monotech/monotech_xt-cf-mini/Images/Front profile.png

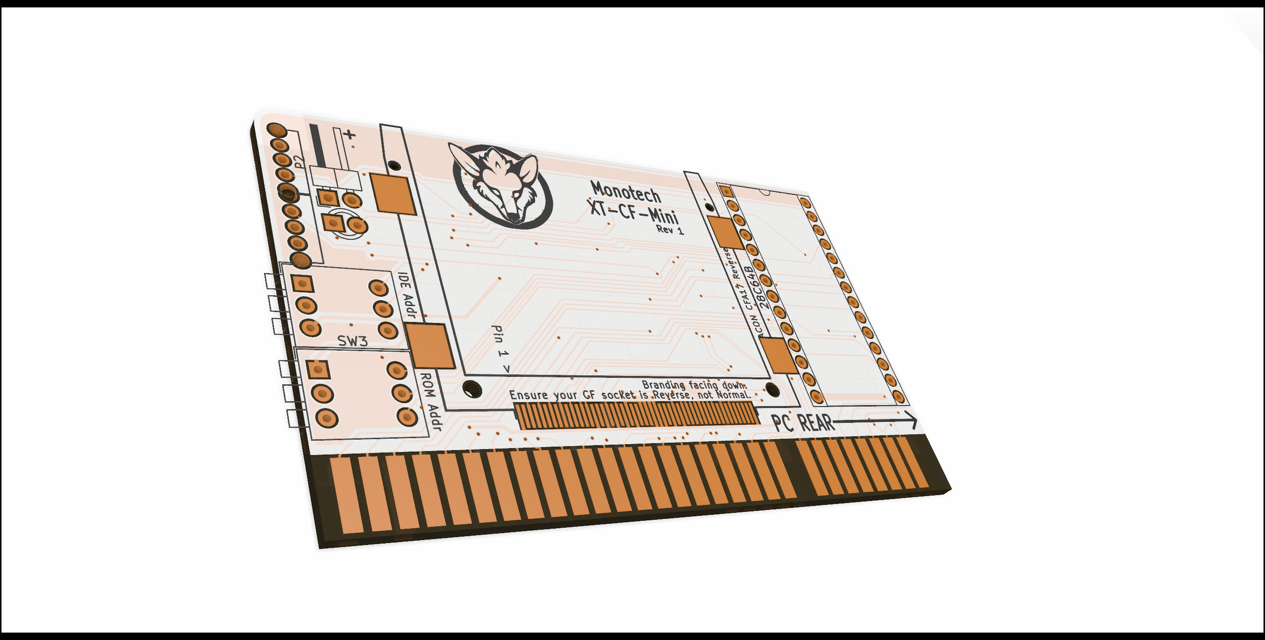
Images/Front profile.png
