monotech/monotech_xt-cf-mini/Photos/Back.jpg

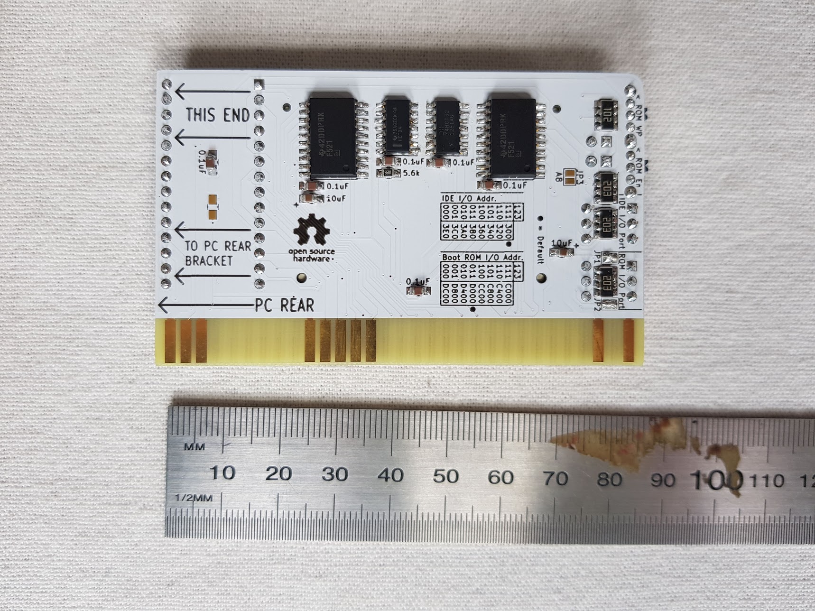
Photos/Back.jpg
