monotech/monotech_xt-cf-mini/Photos/Front.jpg

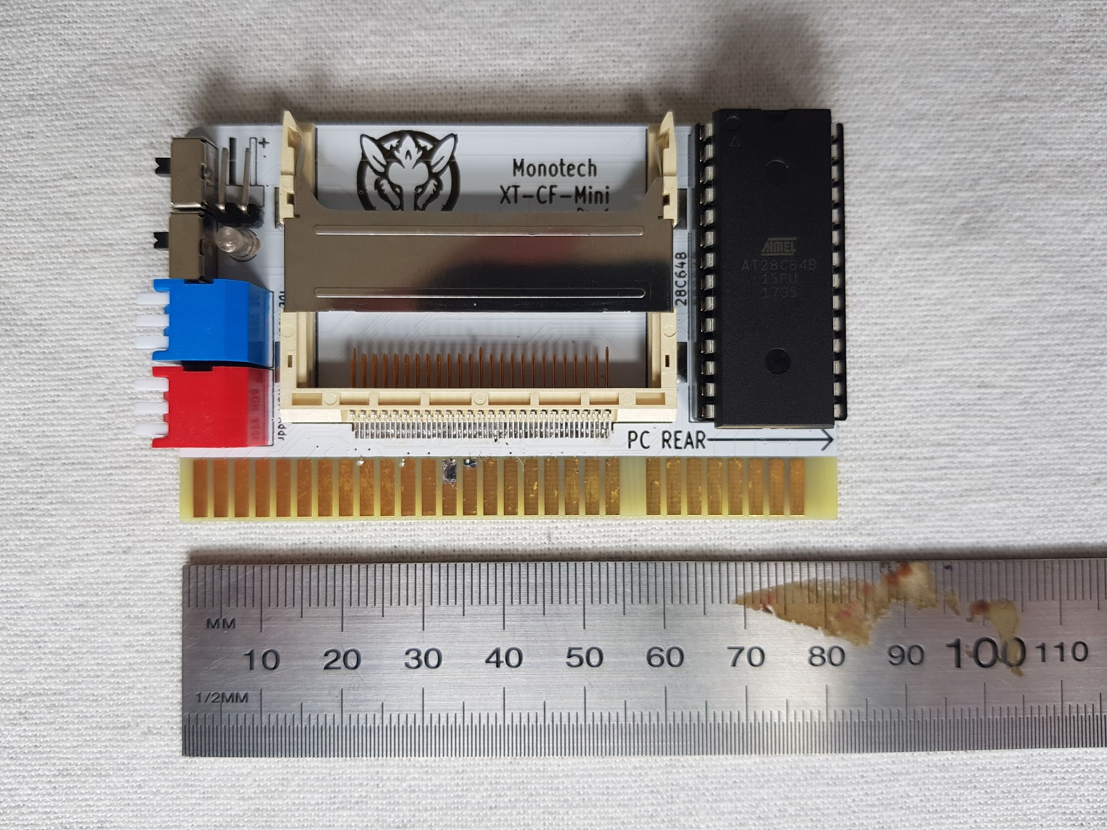
Photos/Front.jpg
