monotech/monotech_xt-cf-mini/Photos/In hand.jpg

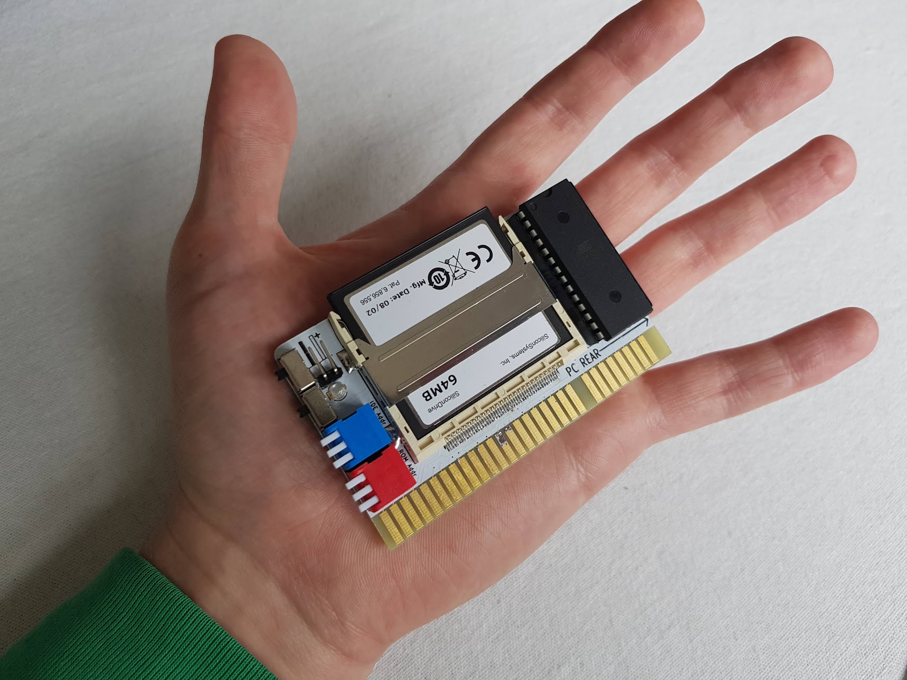
Photos/In hand.jpg
