monotech/monotech_xt-cf-mini/Photos/In motherboard - profile.jpg

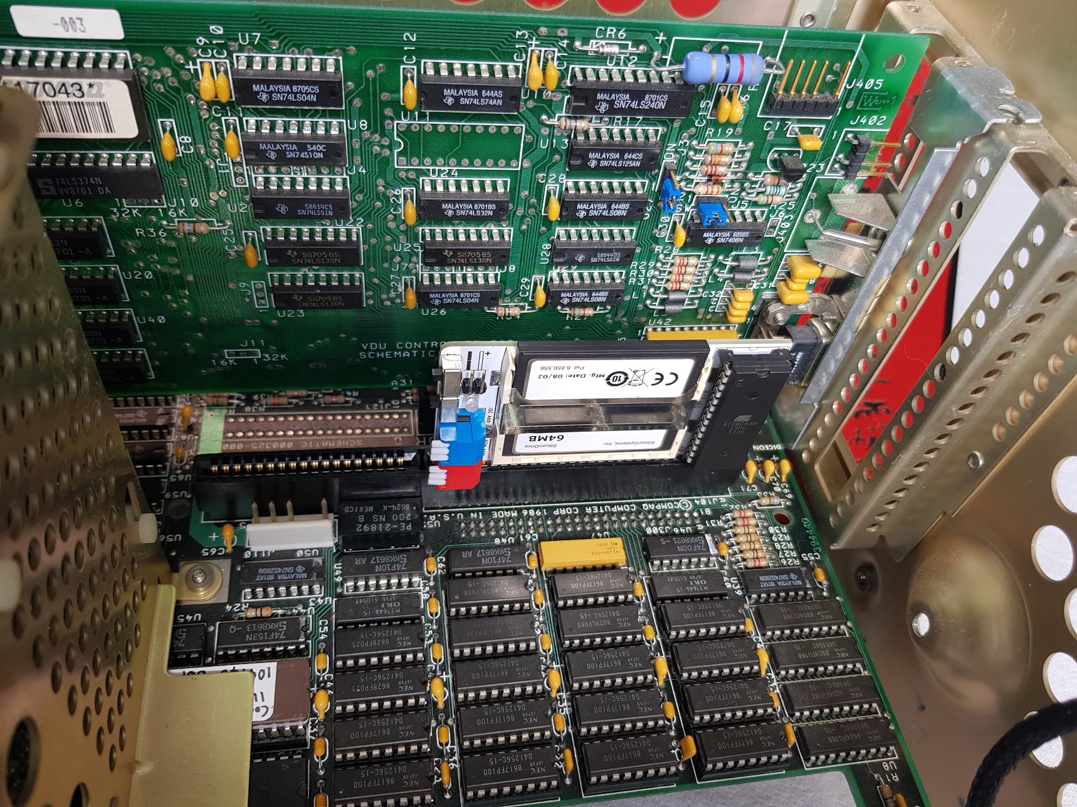
Photos/In motherboard - profile.jpg
