monotech/monotech_xt-cf-mini/Photos/In motherboard - side.jpg

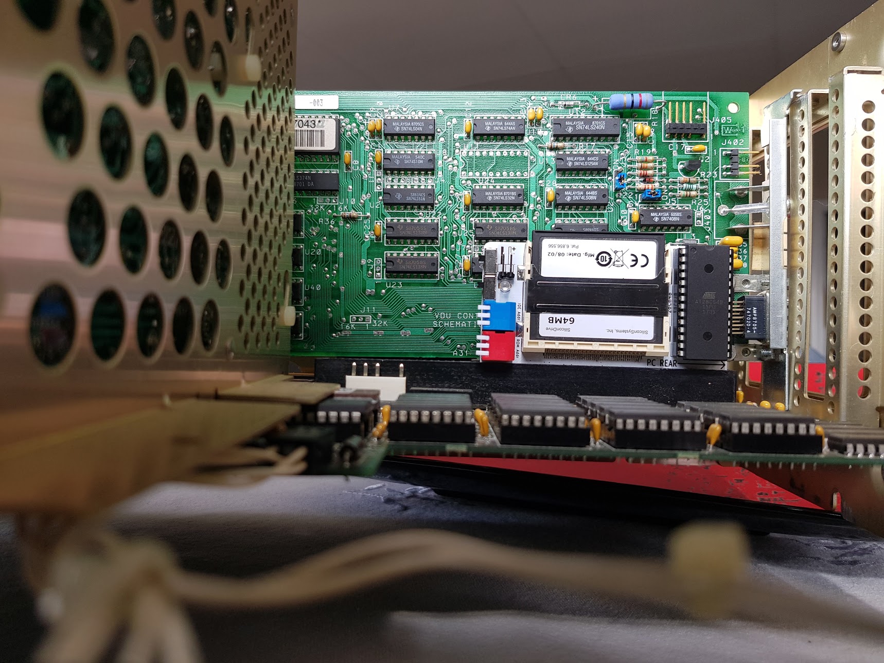
Photos/In motherboard - side.jpg
