monotech/monotech_xt-cf-mini/Images/Front with some parts models.png

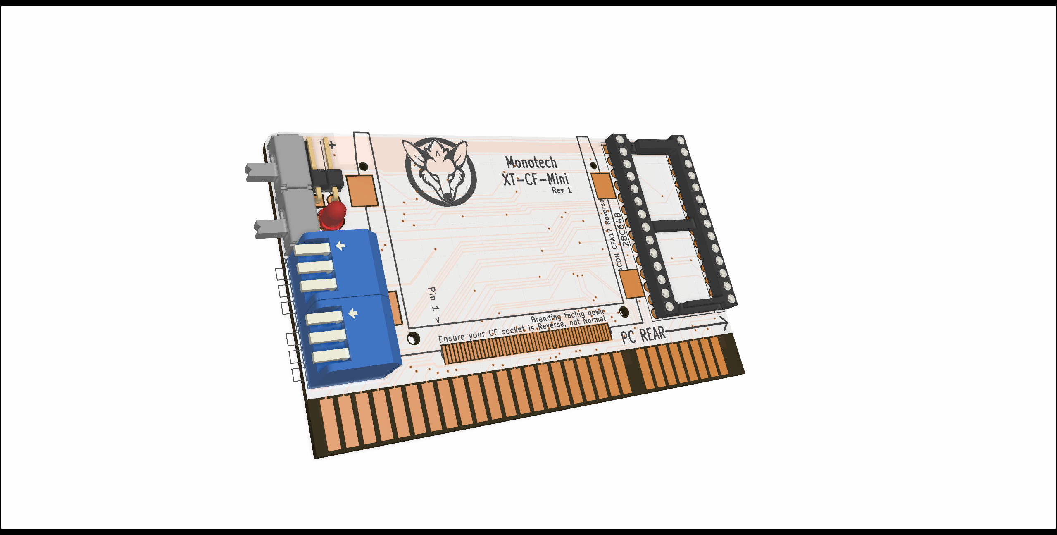
Images/Front with some parts models.png
